jediminer543/JMT-UHF-RFID/Software/Prototype ESP32 Firmware/src/config.h

#ifndef _H_JMTCONFIG
#define _H_JMTCONFIG

uint8_t CC1101_CONFIG[0x2F] = {
  0x29, //GDO
  0x2E, //^
  0x2E, //^
  0x6F, //FIFOTHR
  0xAD, //SYNCWORD
  0x23, //^
  0x01, //PKTLEN
  0x00, //PKTCTRL
  0x02, //^
  0x00, //ADDR
  0x00, //CHANNR
  0x06, //FSCTRL
  0x00, //^
  0x21, //FREQ
  0x4B, //^
  0xD0, //^
  0x7B, //MDMCFG
  0x93, //^
  0x30, //^
  0x23, //^
  0x7A, //^
  0x15, //DEVIANT 
  0x07, //MCSM 
  0x00, //^
  0x18, //^
  0x14, //FOCCFG
  0x6E, //BSCFG
  0x03, //AGCCTRL
  0x40, //^
  0x30, //^
  0x87, //WOREVT
  0x6B, //^
  0xF8, //WORCTRL
  0x56, //FREND
  0x11, //^ CONTAINS PATABLE STUFF
  0xEA, //FSCAL
  0x2A, //^
  0x00, //^
  0x1F, //^ 
  0x41, //RCCTRL
  0x00, //^
  0x59,
  0x7F,
  0x3F,
  0x81,
  0x35,
  0x09
};


#endif
